jessefarrell/WestMacropadWorkshop2025/images/backlight_json.png

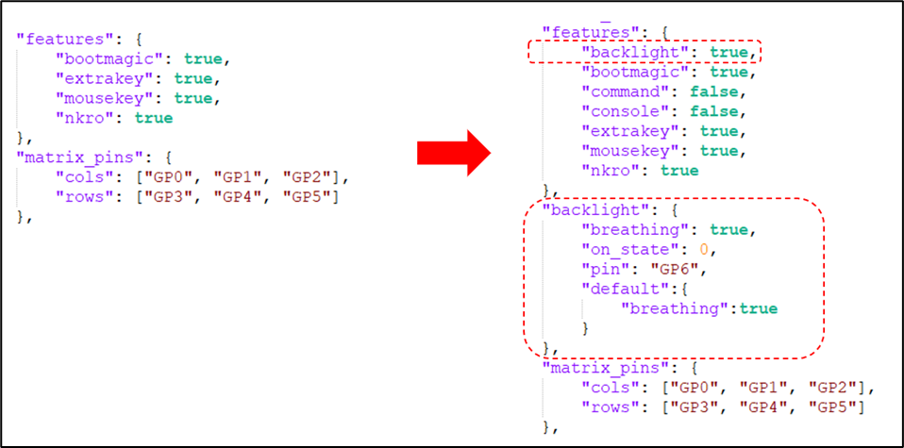
images/backlight_json.png
