jessefarrell/WestMacropadWorkshop2025/images/kicad_symbol_import.png

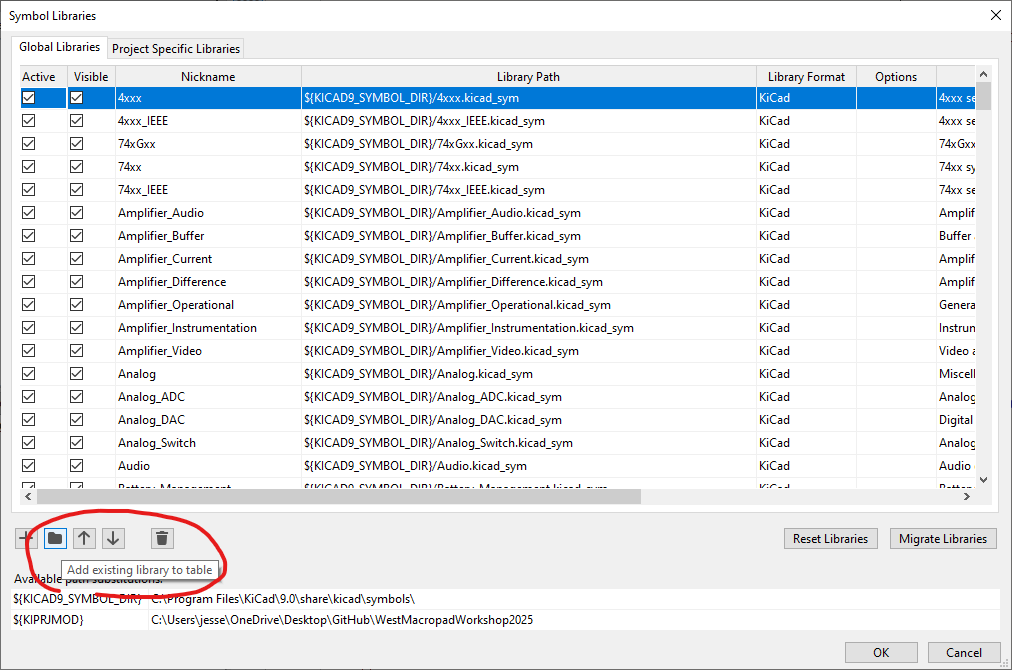
images/kicad_symbol_import.png
