jessefarrell/WestMacropadWorkshop2025/images/layout_edit.png

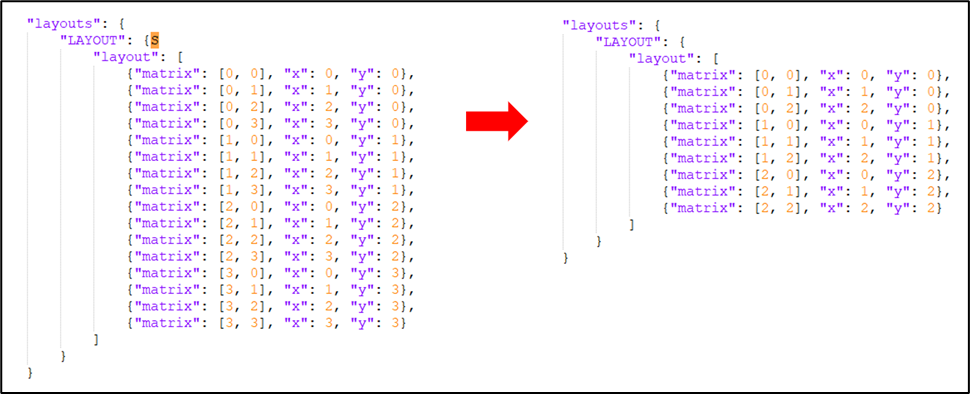
images/layout_edit.png
