jessefarrell/WestMacropadWorkshop2025/design_documents/simulations/ltspice_diode_WEST.asc

D1: diode
D2: diode
R1: res; 100
R2: res; 100
V1: voltage; SINE(0 100 60)
Named nets: Vac, 0, +HalfCycle, -HalfCycle
.tran .1
