jessefarrell/WestMacropadWorkshop2025/design_documents/simulations/ltspice_backlight_driver_WEST.asc

D1: LED
D2: LED
D3: LED
M1: nmos; Si7336ADP
R1: res; 100
R2: res; 100
R3: res; 100
R4: res; 100k
R5: res; 100
V1: voltage; 3.3
V2: voltage; SINE(0 3.3 60)
V3: voltage; PULSE(0 3.3 0 1u 1u 8m 16m)
Named nets: 3V3, SWITCH, 0, Vgate
.tran .1
